ultimaterobotics/uECG_v4_3_all/base_firmware/fast_radio.c

#include "fast_radio.h"
#include "timer_core.h"
#include "nrf.h"

#define PACKET0_S1_SIZE             (8UL)  //!< S1 size in bits
#define PACKET0_S0_SIZE             (1UL)  //!< S0 size in bytes
#define PACKET0_PAYLOAD_SIZE        (8UL)  //!< payload size in bits
#define PACKET1_BASE_ADDRESS_LENGTH (4UL)  //!< base address length in bytes
uint32_t pack_max_length = 64;  //!< static length in bytes
uint32_t pack_payload = 64;  //!< payload size in bytes

uint32_t rx_packet_counter = 0;
uint32_t last_processed_rx_packet = 0;
uint32_t last_end_event_time = 0;
volatile uint32_t last_rx_time = 0;

volatile uint8_t current_mode = 0; // 0 - off, 1 - rx, 2 - tx, 3 - tx->rx
uint8_t rx_packet[256];
uint8_t tx_packet[256];


uint8_t rx_packet_stack[370];
uint32_t rx_packet_stack_times[10];
int rx_packet_stack_q = 37;
int rx_pack_stack_pos = 0;
int rx_pack_stack_len = 10;

enum
{
	rm_rx_end = 1,
	rm_tx_end,
	rm_rx2tx,
	rm_tx2rx,
	rm_rx2rx
};

void fr_disable()
{
	if(NRF_RADIO->STATE == 0) return; //already disabled
	
    NRF_RADIO->SHORTS          = 0;
    NRF_RADIO->EVENTS_DISABLED = 0;
    NRF_RADIO->TASKS_DISABLE   = 1;
    while (NRF_RADIO->EVENTS_DISABLED == 0) ;
    NRF_RADIO->EVENTS_DISABLED = 0;
}

void fr_init(int packet_length)
{
	pack_payload = packet_length;
    // Radio config
    NRF_RADIO->TXPOWER   = (RADIO_TXPOWER_TXPOWER_Pos4dBm << RADIO_TXPOWER_TXPOWER_Pos);
    NRF_RADIO->FREQUENCY = 21UL; 
//    NRF_RADIO->MODE      = (RADIO_MODE_MODE_Nrf_2Mbit << RADIO_MODE_MODE_Pos);
    NRF_RADIO->MODE      = (RADIO_MODE_MODE_Nrf_250Kbit << RADIO_MODE_MODE_Pos);
//    NRF_RADIO->MODE      = (RADIO_MODE_MODE_Nrf_1Mbit << RADIO_MODE_MODE_Pos);

    // Radio address config
    NRF_RADIO->PREFIX0     = 0x44332211UL;  // Prefix byte of addresses 3 to 0
    NRF_RADIO->PREFIX1     = 0x88776655UL;  // Prefix byte of addresses 7 to 4
    NRF_RADIO->BASE0       = 0x0EE60DA7UL;  // Base address for prefix 0
//    NRF_RADIO->BASE1       = 0x0EE6050CUL;  // Base address for prefix 1-7
    NRF_RADIO->BASE1       = 0x0EE60DA7UL;  // Base address for prefix 1-7
    NRF_RADIO->TXADDRESS   = 0x0UL;        // Set device address 0 to use when transmitting
    NRF_RADIO->RXADDRESSES = 0b00000001;        // receive on address 0

    // Packet configuration
    NRF_RADIO->PCNF0 = (PACKET0_S1_SIZE << RADIO_PCNF0_S1LEN_Pos) |
                       (PACKET0_S0_SIZE << RADIO_PCNF0_S0LEN_Pos) |
                       (pack_payload << RADIO_PCNF0_LFLEN_Pos); //lint !e845 "The right argument to operator '|' is certain to be 0"

    // Packet configuration
    NRF_RADIO->PCNF1 = (RADIO_PCNF1_WHITEEN_Disabled << RADIO_PCNF1_WHITEEN_Pos) |
                       (RADIO_PCNF1_ENDIAN_Big << RADIO_PCNF1_ENDIAN_Pos)        |
                       (PACKET1_BASE_ADDRESS_LENGTH << RADIO_PCNF1_BALEN_Pos)    |
                       (pack_max_length << RADIO_PCNF1_STATLEN_Pos)        |
                       (pack_payload << RADIO_PCNF1_MAXLEN_Pos); //lint !e845 "The right argument to operator '|' is certain to be 0"

    // CRC Config
	NRF_RADIO->CRCCNF = (RADIO_CRCCNF_LEN_One << RADIO_CRCCNF_LEN_Pos); // Number of checksum bits
	NRF_RADIO->CRCINIT = 0b10101010;   // Initial value
	NRF_RADIO->CRCPOLY = 0b100000111;  // CRC poly: x^8+x^2+x^1+1
	
	NRF_RADIO->INTENSET = 0b01000; //END event
//	NRF_RADIO->INTENSET = 0b01010; //END & ADDRESS events
	NVIC_EnableIRQ(RADIO_IRQn);
}

void fr_ble_mode(uint8_t channel)
{
	NRF_RADIO->POWER = 1;
  // Configure radio with 2Mbit Nordic proprietary mode
//  NRF_RADIO->MODE = RADIO_MODE_MODE_Nrf_2Mbit << RADIO_MODE_MODE_Pos;
  
	NRF_RADIO->MODE = RADIO_MODE_MODE_Ble_1Mbit << RADIO_MODE_MODE_Pos;

	if(channel == 37) NRF_RADIO->FREQUENCY = 2;  //26, 80 other channels
	if(channel == 38) NRF_RADIO->FREQUENCY = 26;
	if(channel == 39) NRF_RADIO->FREQUENCY = 80;
	NRF_RADIO->DATAWHITEIV = channel;
	
  NRF_RADIO->PCNF0 = (
    (((1UL) << RADIO_PCNF0_S0LEN_Pos) & RADIO_PCNF0_S0LEN_Msk) |  /* Length of S0 field in bytes 0-1.    */
    (((2UL) << RADIO_PCNF0_S1LEN_Pos) & RADIO_PCNF0_S1LEN_Msk) |  /* Length of S1 field in bits 0-8.     */
    (((6UL) << RADIO_PCNF0_LFLEN_Pos) & RADIO_PCNF0_LFLEN_Msk)    /* Length of length field in bits 0-8. */
  );

  /* Packet configuration */
  NRF_RADIO->PCNF1 = (
    (((37UL) << RADIO_PCNF1_MAXLEN_Pos) & RADIO_PCNF1_MAXLEN_Msk)   |                      /* Maximum length of payload in bytes [0-255] */
    (((0UL) << RADIO_PCNF1_STATLEN_Pos) & RADIO_PCNF1_STATLEN_Msk)   |                      /* Expand the payload with N bytes in addition to LENGTH [0-255] */
    (((3UL) << RADIO_PCNF1_BALEN_Pos) & RADIO_PCNF1_BALEN_Msk)       |                      /* Base address length in number of bytes. */
    (((RADIO_PCNF1_ENDIAN_Little) << RADIO_PCNF1_ENDIAN_Pos) & RADIO_PCNF1_ENDIAN_Msk) |  /* Endianess of the S0, LENGTH, S1 and PAYLOAD fields. */
    (((1UL) << RADIO_PCNF1_WHITEEN_Pos) & RADIO_PCNF1_WHITEEN_Msk)                         /* Enable packet whitening */
  );

	// Configure packet with no S0,S1 or Length fields and 8-bit preamble.
	NRF_RADIO->PCNF0 = (6 << RADIO_PCNF0_LFLEN_Pos) |
			(1 << RADIO_PCNF0_S0LEN_Pos) |
			(2 << RADIO_PCNF0_S1LEN_Pos); 

//			(RADIO_PCNF0_S1INCL_Automatic << RADIO_PCNF0_S1INCL_Pos) |
//			(RADIO_PCNF0_PLEN_8bit << RADIO_PCNF0_PLEN_Pos);
  
//	NRF_RADIO->PCNF0 = (((1UL) << RADIO_PCNF0_S0LEN_Pos) & RADIO_PCNF0_S0LEN_Msk) |  /* Length of S0 field in bytes 0-1.    */
//		(((2UL) << RADIO_PCNF0_S1LEN_Pos) & RADIO_PCNF0_S1LEN_Msk) |  /* Length of S1 field in bits 0-8.     */
//		(((6UL) << RADIO_PCNF0_LFLEN_Pos) & RADIO_PCNF0_LFLEN_Msk);    /* Length of length field in bits 0-8. */

	// Configure static payload length. 4 bytes address, little endian with whitening enabled.
	NRF_RADIO->PCNF1 =  (37 << RADIO_PCNF1_MAXLEN_Pos) |
			(0 << RADIO_PCNF1_STATLEN_Pos) |
			(3  << RADIO_PCNF1_BALEN_Pos) | 
			(RADIO_PCNF1_ENDIAN_Little << RADIO_PCNF1_ENDIAN_Pos) |
			(RADIO_PCNF1_WHITEEN_Enabled << RADIO_PCNF1_WHITEEN_Pos);

	// Configure address Prefix0 + Base0
	//0x8E89BED6 - bed 6 advertising address
	NRF_RADIO->BASE0   = 0x89BED600;
	NRF_RADIO->PREFIX0 = 0x8E;// << RADIO_PREFIX0_AP0_Pos;

	// Use logical address 0 (BASE0 + PREFIX0 byte 0)
	NRF_RADIO->TXADDRESS = 0;// << RADIO_TXADDRESS_TXADDRESS_Pos;
	NRF_RADIO->RXADDRESSES = 1;// << RADIO_TXADDRESS_TXADDRESS_Pos;
  
	// Initialize CRC
//	NRF_RADIO->CRCCNF = (RADIO_CRCCNF_LEN_Three << RADIO_CRCCNF_LEN_Pos) |
//			(RADIO_CRCCNF_SKIPADDR_Skip << RADIO_CRCCNF_SKIPADDR_Pos);
	NRF_RADIO->CRCCNF = (RADIO_CRCCNF_LEN_Three << RADIO_CRCCNF_LEN_Pos) |
			(RADIO_CRCCNF_SKIPADDR_Skip << RADIO_CRCCNF_SKIPADDR_Pos);

	NRF_RADIO->CRCPOLY = 0x00065B;
	NRF_RADIO->CRCINIT = 0x555555;
  

  // Enable fast rampup, new in nRF52
//  NRF_RADIO->MODECNF0 = (RADIO_MODECNF0_DTX_B0 << RADIO_MODECNF0_DTX_Pos) |
//                        (RADIO_MODECNF0_RU_Fast << RADIO_MODECNF0_RU_Pos);
                        
	// 4dBm output power
	NRF_RADIO->TXPOWER = RADIO_TXPOWER_TXPOWER_0dBm << RADIO_TXPOWER_TXPOWER_Pos;
	NRF_RADIO->EVENTS_DISABLED = 0;
	NRF_RADIO->EVENTS_END = 0;
	NRF_RADIO->EVENTS_READY = 0;
	NRF_RADIO->EVENTS_ADDRESS = 0;	
	
	for(int x = 0; x < 64; x++) rx_packet[x] = 0;
	
	NRF_RADIO->INTENSET = 0b01000; //END event
	NVIC_EnableIRQ(RADIO_IRQn);	
	
}

void fr_mode_rx_only()
{
	if(NRF_RADIO->STATE & 0b01000) fr_disable(); //tx state
	else if(!(NRF_RADIO->STATE & 0b011)) fr_disable(); //states 1, 2, 3 responsible for RX
	
	NRF_RADIO->POWER = 1;
//	NRF_RADIO->SHORTS = RADIO_SHORTS_READY_START_Msk | RADIO_SHORTS_END_DISABLE_Msk | RADIO_SHORTS_ADDRESS_RSSISTART_Msk;
	NRF_RADIO->SHORTS = RADIO_SHORTS_READY_START_Msk | RADIO_SHORTS_ADDRESS_RSSISTART_Msk;
	NRF_RADIO->EVENTS_READY = 0;
	NRF_RADIO->TASKS_RXEN = 1;
	current_mode = rm_rx2rx;
}
void fr_mode_tx_only()
{
	if(!(NRF_RADIO->STATE & 0b01000)) fr_disable(); //non-tx state
	else if(!(NRF_RADIO->STATE & 0b011)) fr_disable(); //states 9, 10, 11 responsible for TX
	NRF_RADIO->POWER = 1;
	
	NRF_RADIO->SHORTS = RADIO_SHORTS_READY_START_Msk | RADIO_SHORTS_END_DISABLE_Msk | RADIO_SHORTS_ADDRESS_RSSISTART_Msk;
	NRF_RADIO->TASKS_TXEN = 1;
	current_mode = rm_tx_end;
}
void fr_mode_tx_then_rx()
{
	if(!(NRF_RADIO->STATE & 0b01000)) fr_disable(); //non-tx state
	else if(!(NRF_RADIO->STATE & 0b011)) fr_disable(); //states 9, 10, 11 responsible for TX
//	fr_disable();
	NRF_RADIO->POWER = 1;
	NRF_RADIO->SHORTS = RADIO_SHORTS_READY_START_Msk | RADIO_SHORTS_END_DISABLE_Msk | RADIO_SHORTS_ADDRESS_RSSISTART_Msk;
	NRF_RADIO->TASKS_TXEN = 1;
	for(int x = 0; x < 20; x++) ; //to make sure radio enters TXEN sequence before enabling DISABLED_RXEN shortcut
	NRF_RADIO->SHORTS |= RADIO_SHORTS_DISABLED_RXEN_Msk;
//	NRF_RADIO->INTENSET = RADIO_INTENSET_END_Msk;
	current_mode = rm_tx2rx;
}

void fr_send(uint8_t *pack)
{
	for(int x = 0; x < pack_payload; x++)
		tx_packet[x] = pack[x];
	NRF_RADIO->PACKETPTR = (uint32_t)tx_packet;
	fr_mode_tx_only();
}
void fr_listen()
{
	last_processed_rx_packet = rx_packet_counter;
	NRF_RADIO->PACKETPTR = (uint32_t)rx_packet;
	fr_mode_rx_only();
//	NRF_RADIO->INTENSET = RADIO_INTENSET_END_Msk;
}
void fr_send_and_listen(uint8_t *pack)
{
	for(int x = 0; x < pack_payload; x++)
		tx_packet[x] = pack[x];
	NRF_RADIO->PACKETPTR = (uint32_t)tx_packet;
	fr_mode_tx_then_rx();
}
int fr_has_new_packet()
{
	return (last_processed_rx_packet != rx_packet_counter);
}
uint32_t fr_get_packet(uint8_t *pack)
{
	for(int x = 0; x < pack_payload; x++)
		pack[x] = rx_packet[x];
//	pack = rx_packet;
	last_processed_rx_packet = rx_packet_counter;
	return last_rx_time;
}

int last_processed_stack = 0;

int fr_has_new_packet2()
{
	if(last_processed_stack != rx_pack_stack_pos) return 1;
	return 0;
}
uint32_t fr_get_packet2(uint8_t *pack)
{
	int s = last_processed_stack;
	last_processed_stack++;
	if(last_processed_stack >= 10) last_processed_stack = 0;

	for(int x = 0; x < rx_packet_stack_q; x++)
		pack[x] = rx_packet_stack[s*rx_packet_stack_q + x];

	return rx_packet_stack_times[s];
}

void push_rx_pack()
{
	int s = rx_pack_stack_pos;
	for(int x = 0; x < rx_packet_stack_q; x++)
		rx_packet_stack[s*rx_packet_stack_q + x] = rx_packet[x];
	rx_packet_stack_times[s] = last_rx_time;
	rx_pack_stack_pos++;
	if(rx_pack_stack_pos >= 10) rx_pack_stack_pos = 0;
}

uint32_t irq_cnt = 0;

void RADIO_IRQHandler()
{
	irq_cnt++;
	if(NRF_RADIO->EVENTS_END)// && (NRF_RADIO->INTENSET & RADIO_INTENSET_END_Msk))
	{
		NRF_RADIO->EVENTS_END = 0;
		last_end_event_time = micros();
		if(current_mode == rm_rx_end || current_mode == rm_rx2rx || current_mode == rm_rx2tx)
		{
			rx_packet_counter++;
			last_rx_time = last_end_event_time;
			push_rx_pack();
			if(current_mode == rm_rx2tx)
			{
				if(0)//NRF_RADIO->CRCSTATUS != 0)
				{
					tx_packet[0] = 111;
					tx_packet[1] = 111;
					tx_packet[2] = 111;
					tx_packet[3] = 111;
					while (NRF_RADIO->EVENTS_DISABLED == 0) ;
					NRF_RADIO->EVENTS_DISABLED = 0;
					
					current_mode = rm_tx2rx;
					NRF_RADIO->PACKETPTR = (uint32_t)tx_packet;
					NRF_RADIO->SHORTS = RADIO_SHORTS_READY_START_Msk | RADIO_SHORTS_END_DISABLE_Msk | RADIO_SHORTS_ADDRESS_RSSISTART_Msk;
					NRF_RADIO->TASKS_TXEN = 1;
					for(int volatile t = 0; t < 20; t++) t++;
					NRF_RADIO->SHORTS |= RADIO_SHORTS_DISABLED_RXEN_Msk;
					
//					fr_mode_rx_only();
//					fr_mode_tx_then_rx();
				}
				else
				{
					NRF_RADIO->TASKS_RXEN = 1;
				}
//					fr_mode_rx_only();
			}
			else if(current_mode == rm_rx2rx)
			{
//				while (NRF_RADIO->EVENTS_DISABLED == 0) ;
//				NRF_RADIO->EVENTS_DISABLED = 0;
//				NRF_RADIO->TASKS_RXEN = 1;
				NRF_RADIO->TASKS_START = 1;
			}
			
		}
		else if(current_mode == rm_tx2rx) //tx event ended, switched to rx using shorts
		{
			NRF_RADIO->PACKETPTR = (uint32_t)rx_packet;
			current_mode = rm_rx2tx;
			while (NRF_RADIO->EVENTS_DISABLED == 0) ;
			NRF_RADIO->EVENTS_DISABLED = 0;
			NRF_RADIO->TASKS_RXEN = 1;
			
//			NRF_RADIO->PACKETPTR = (uint32_t)rx_packet;
//			current_mode = 1;
		}
	}
}

uint32_t fr_get_irq_cnt()
{
	return irq_cnt;
}
